Lawrence4U/Irrigation-System-LoRa-TFG/KiCAD Files/TestingSizes/TestingSizes.kicad_pcb

## KiCad design IBM31SD.kicad_sch

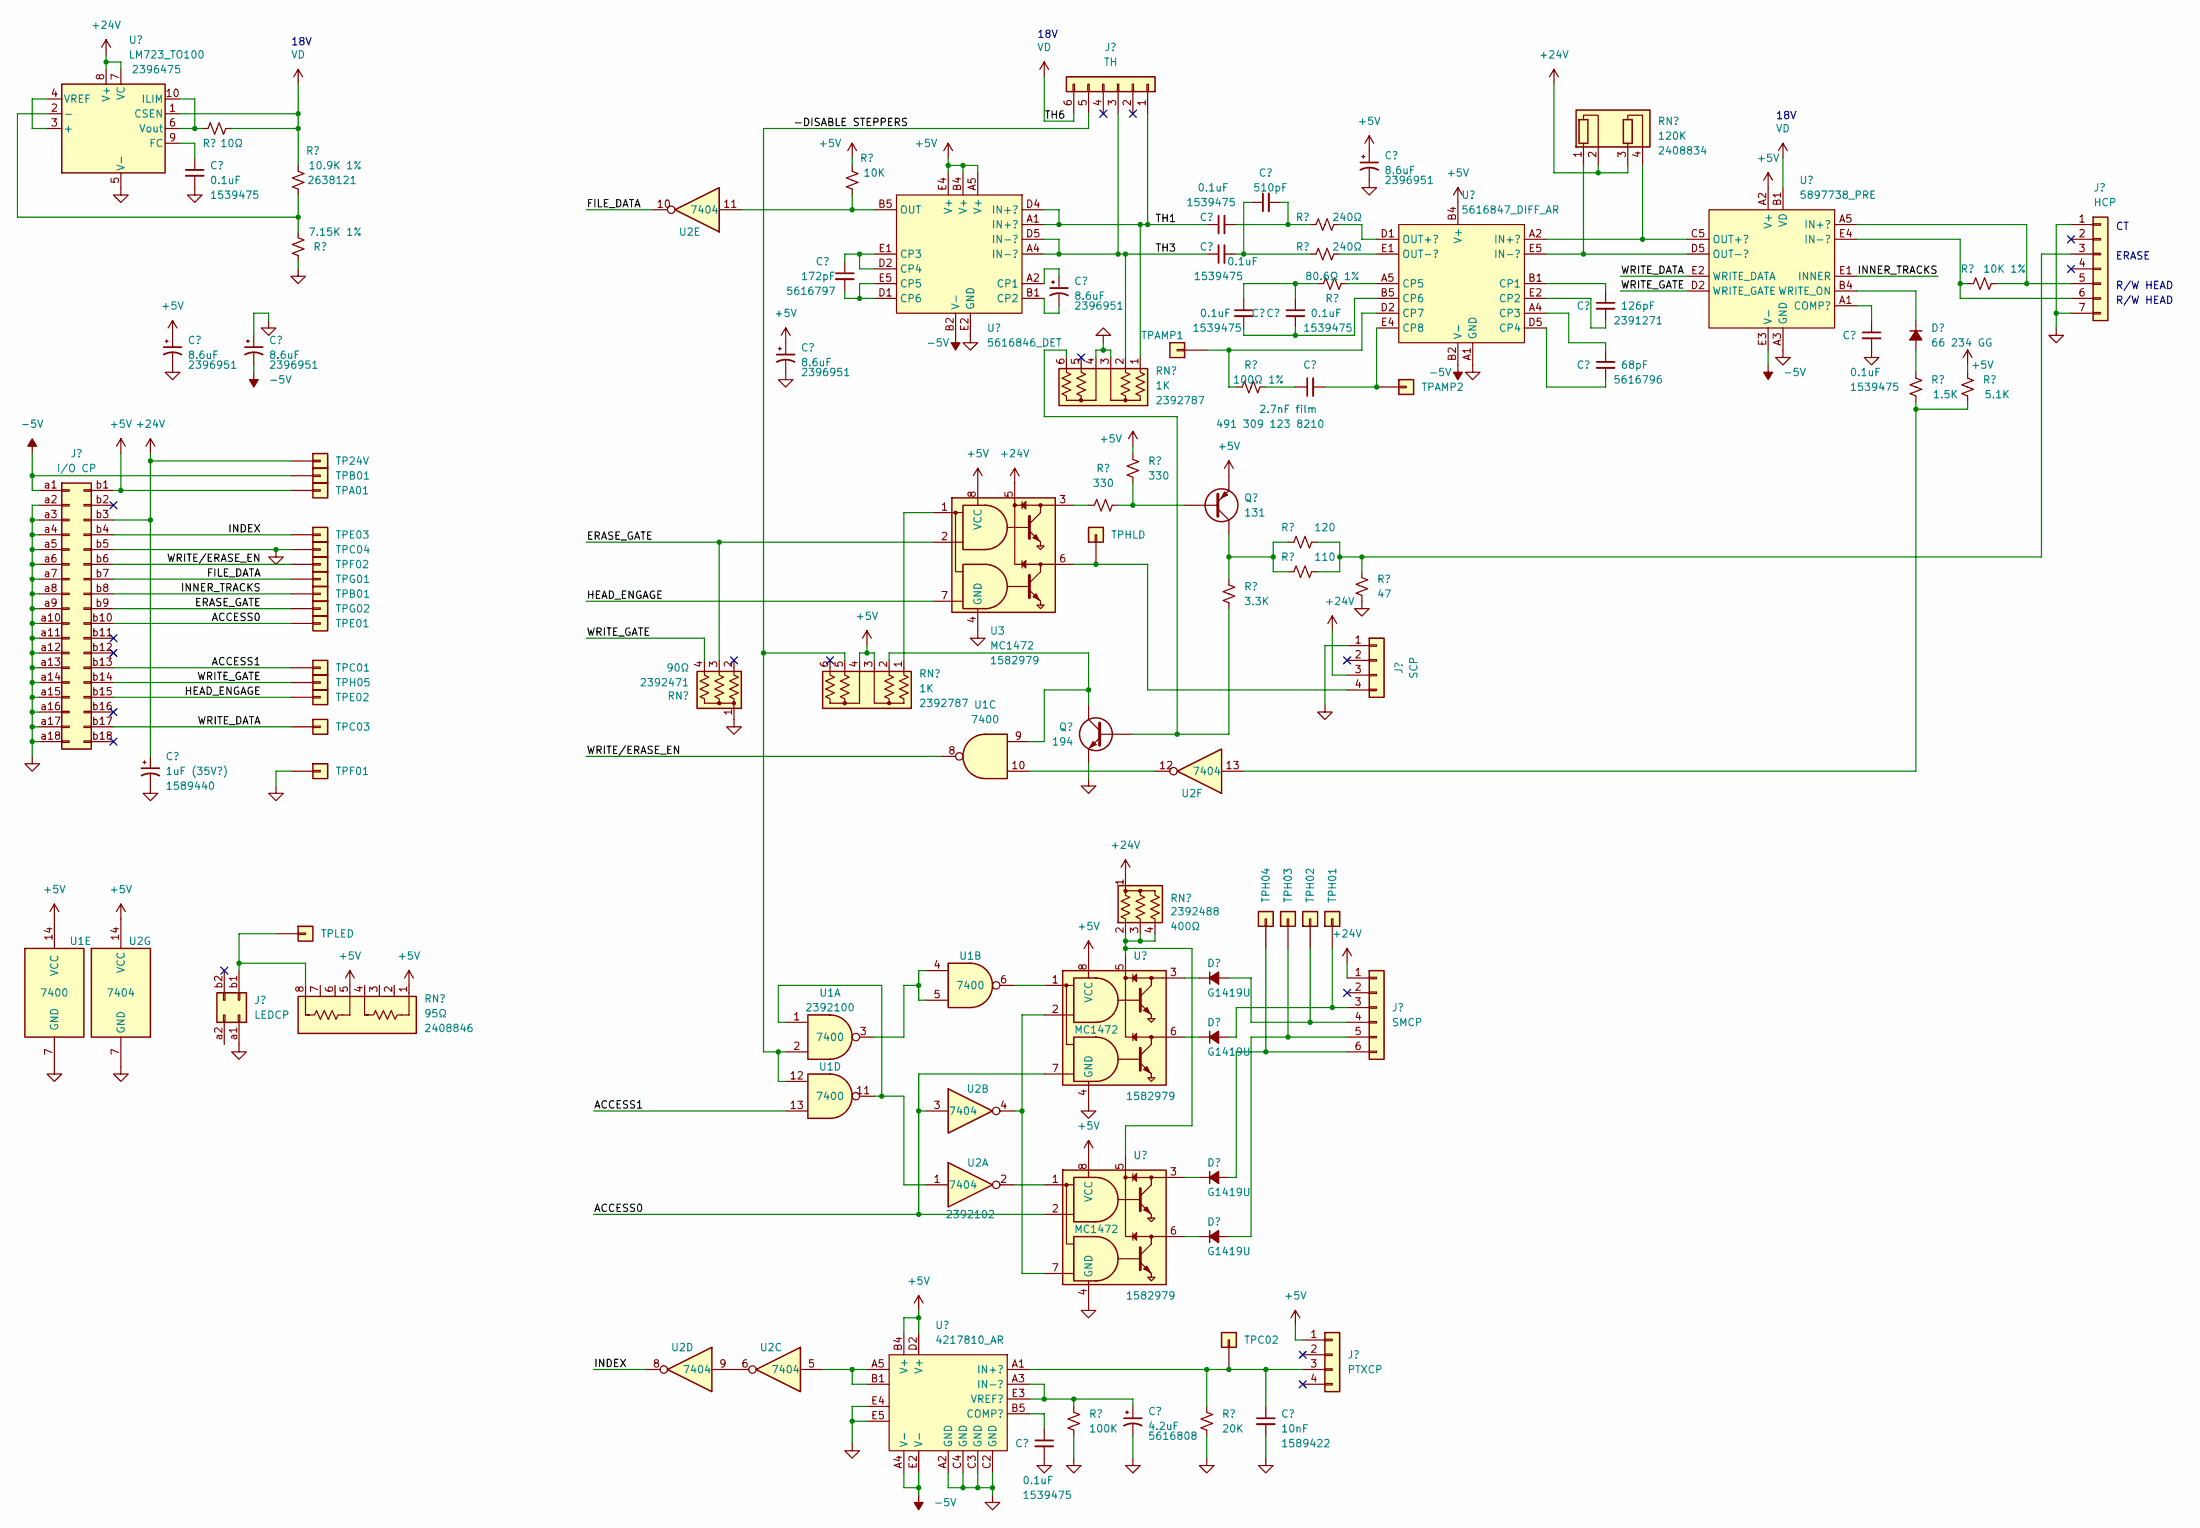
[picture p4: schematic IBM31SD.kicad_sch]

Parts:
TP24V: Conn_01x01
TPA01: Conn_01x01
TPAMP1, TPAMP2: Conn_01x01
TPB01: Conn_01x01
TPC01, TPC02, TPC03, TPC04: Conn_01x01
TPE01, TPE02, TPE03: Conn_01x01
TPF01, TPF02: Conn_01x01
TPG01, TPG02: Conn_01x01
TPH01, TPH02, TPH03, TPH04, TPH05: Conn_01x01
TPHLD: Conn_01x01
TPLED: Conn_01x01
U1: 7400
U2: 7404
U3: MC1472

Connections:
-DISABLE STEPPERS: U1.2, U1.12
ACCESS0: TPE01.1, U2.3
ACCESS1: TPC01.1, U1.13
ERASE_GATE: TPG02.1, U3.2
FILE_DATA: TPG01.1, U2.10
HEAD_ENGAGE: TPE02.1, U3.7
INDEX: TPE03.1, U2.8
INNER_TRACKS: TPB01.1
unnamed: TPHLD.1, U3.6
unnamed: U1.1, U1.11, U2.1
unnamed: U1.3, U1.4, U1.5
unnamed: U1.10, U2.12
unnamed: U2.6, U2.9
WRITE_DATA: TPC03.1
WRITE_GATE: TPH05.1
WRITE/ERASE_EN: TPF02.1, U1.8

Notes on the sheet:
18V
R/W HEAD
ERASE
