Lawrence4U/Irrigation-System-LoRa-TFG/LoraSendAndReceiveUpdated_3/arduino_secrets.h

// Replace with keys obtained from TheThingsNetwork console
#define SECRET_APP_EUI "0000000000000000"
//#define SECRET_APP_KEY "0708CDD83E2D375D7ACE1D7F9C82AF20" // Cuenta de Lorenzo
#define SECRET_APP_KEY "59DFFF0E6122749AF1CC76950FF0BDF2" // Cuenta de INEA-ICAI
